pweber22/pumpkin-computer/PumpkinComputer/Pumpkin.h

static const float pumpkin_cd=1.00; // coefficient of drag of the pumpkin
static const float pumpkin_mass=0.830;  // mass of the pumpkin in kg
static const float pumpkin_circumference=0.40;  // circumference of the pumpkin in meters
