pweber22/pumpkin-computer/PumpkinComputer/Display.h

static const uint8_t image_data_frame000[256] PROGMEM = {
    0x00, 0x00, 0x00, 0x00, 0x00, 0x00, 0x00, 0x00, 
    0x00, 0x00, 0x00, 0x00, 0x00, 0x00, 0x00, 0x00, 
    0x00, 0x00, 0x00, 0x00, 0x0a, 0x80, 0x00, 0x00, 
    0x00, 0x00, 0x00, 0x00, 0x55, 0x60, 0x00, 0x00, 
    0x00, 0x00, 0x00, 0x01, 0x24, 0x90, 0x00, 0x00, 
    0x00, 0x00, 0x00, 0x04, 0x92, 0x54, 0x00, 0x00, 
    0x00, 0x00, 0x00, 0x12, 0xaa, 0x90, 0x00, 0x00, 
    0x03, 0x00, 0x00, 0x4e, 0xa9, 0x40, 0x00, 0x00, 
    0x01, 0x00, 0x01, 0x2d, 0x25, 0x00, 0x00, 0x00, 
    0x02, 0x00, 0x14, 0xac, 0x94, 0x00, 0x00, 0x00, 
    0x06, 0x00, 0x75, 0x5a, 0xa0, 0x00, 0x00, 0x00, 
    0x02, 0x00, 0x59, 0x72, 0x40, 0x00, 0x00, 0x00, 
    0x04, 0x00, 0x30, 0xe9, 0x00, 0x00, 0x00, 0x00, 
    0x04, 0x00, 0x33, 0xfe, 0x00, 0x00, 0x01, 0xa0, 
    0x08, 0xf4, 0x03, 0xbf, 0xc0, 0x00, 0x01, 0xf0, 
    0x09, 0x7f, 0xae, 0xdf, 0xf0, 0x00, 0x03, 0xf8, 
    0x18, 0xaf, 0xf6, 0x2f, 0xfc, 0x00, 0x03, 0xf0, 
    0x11, 0x2a, 0xff, 0xd3, 0xff, 0x80, 0x07, 0xf8, 
    0x30, 0x15, 0xbf, 0xf8, 0x7f, 0xf0, 0x0f, 0xf8, 
    0x10, 0x02, 0xea, 0xbf, 0x8f, 0xfc, 0x0f, 0xf0, 
    0x00, 0x00, 0x75, 0x6f, 0xf1, 0x7f, 0x3f, 0xf8, 
    0x00, 0x01, 0x79, 0x24, 0xae, 0xaf, 0xff, 0xf8, 
    0x00, 0x00, 0x7a, 0x92, 0xb5, 0xab, 0xd5, 0x20, 
    0x00, 0x02, 0xf0, 0x08, 0x4a, 0xb4, 0x49, 0x54, 
    0x00, 0x01, 0xf8, 0x01, 0x00, 0x95, 0xa5, 0x7a, 
    0x00, 0x05, 0xfe, 0x00, 0x02, 0x02, 0x54, 0xf8, 
    0x00, 0x01, 0x7e, 0x00, 0x00, 0x00, 0x02, 0x10, 
    0x00, 0x28, 0xaa, 0x00, 0x00, 0x00, 0x00, 0x40, 
    0x00, 0x04, 0x00, 0x00, 0x00, 0x00, 0x00, 0x20, 
    0x00, 0x11, 0x00, 0x00, 0x00, 0x00, 0x00, 0x10, 
    0x00, 0x00, 0x00, 0x00, 0x00, 0x00, 0x00, 0x00, 
    0x00, 0x00, 0x00, 0x00, 0x00, 0x00, 0x00, 0x00
};
