pweber22/pumpkin-computer/PumpkinComputer/TargetExample.h

//Rename this file Target.h

double targetLat = 41.917004; // target latitude in decimal degrees
double targetLon = -91.443742;  // target longitude in decimal degrees
int targetAlt_ft = 805;  // target altitude in feet MSL
int bearing = 276; // bearing of the flight path over the target
